StrikeEagleCC/ISU_ITec_Custom_CR-10/Arduino Windows Preconfigured/examples/01.Basics/DigitalReadSerial/layout.png

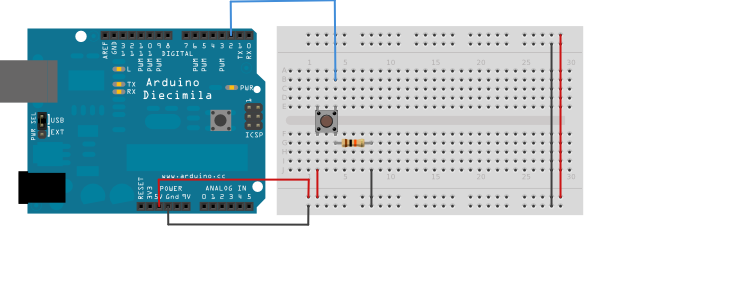
Arduino Windows Preconfigured/examples/01.Basics/DigitalReadSerial/layout.png
