StrikeEagleCC/ISU_ITec_Custom_CR-10/Arduino Windows Preconfigured/examples/01.Basics/Fade/layout.png

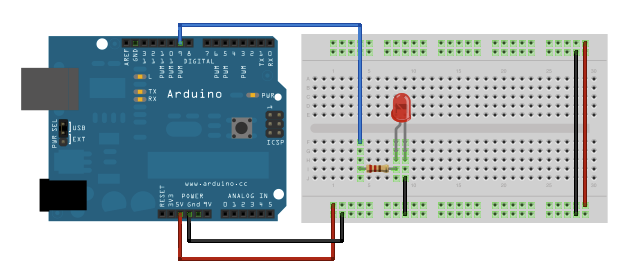
Arduino Windows Preconfigured/examples/01.Basics/Fade/layout.png
