StrikeEagleCC/ISU_ITec_Custom_CR-10/Arduino Windows Preconfigured/examples/02.Digital/toneKeyboard/schematic.png

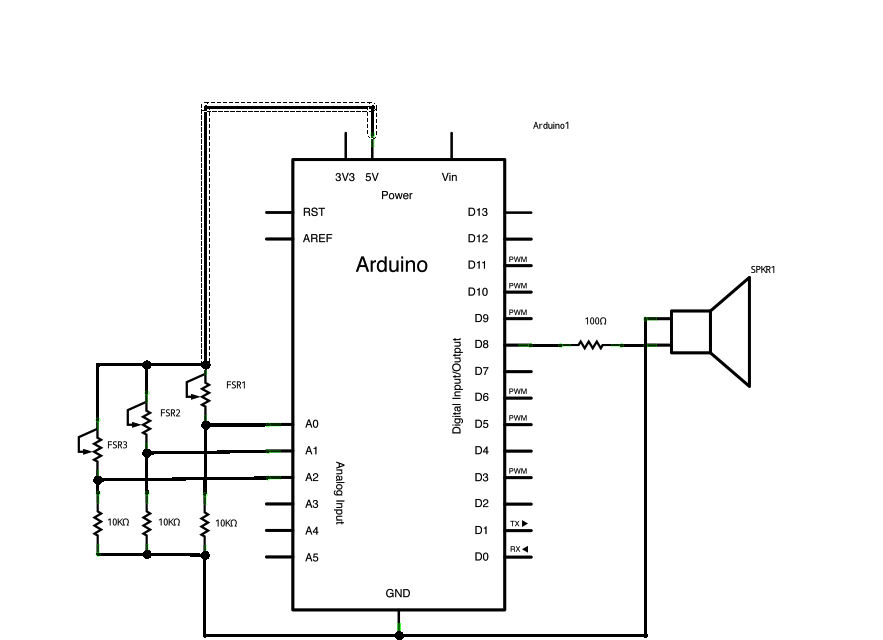
Arduino Windows Preconfigured/examples/02.Digital/toneKeyboard/schematic.png
