StrikeEagleCC/ISU_ITec_Custom_CR-10/Arduino Windows Preconfigured/examples/03.Analog/AnalogInOutSerial/schematic.png

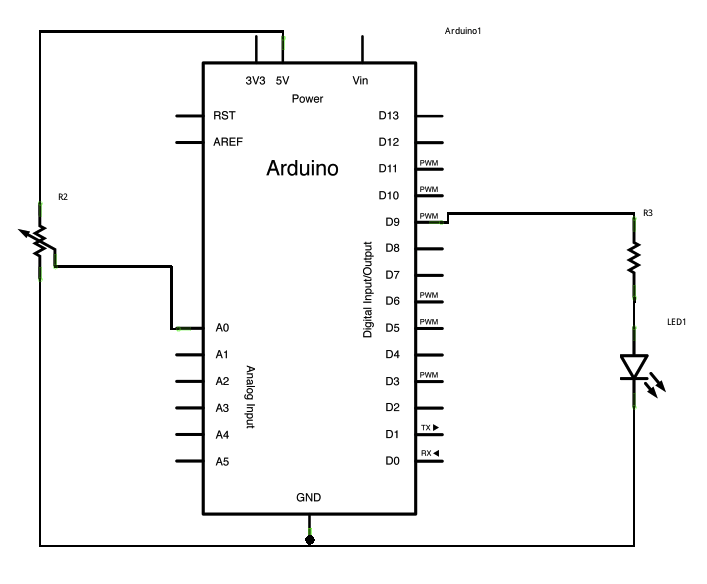
Arduino Windows Preconfigured/examples/03.Analog/AnalogInOutSerial/schematic.png
