StrikeEagleCC/ISU_ITec_Custom_CR-10/Arduino Windows Preconfigured/examples/03.Analog/AnalogWriteMega/schematic.png

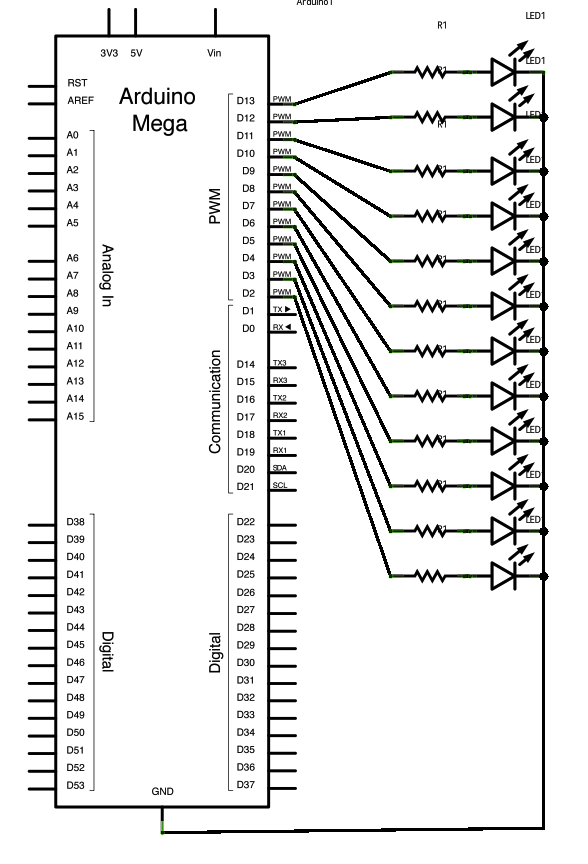
Arduino Windows Preconfigured/examples/03.Analog/AnalogWriteMega/schematic.png
