StrikeEagleCC/ISU_ITec_Custom_CR-10/Arduino Windows Preconfigured/examples/04.Communication/Midi/layout.png

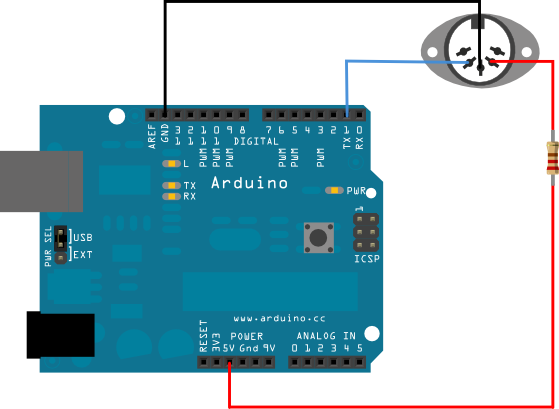
Arduino Windows Preconfigured/examples/04.Communication/Midi/layout.png
