StrikeEagleCC/ISU_ITec_Custom_CR-10/Arduino Windows Preconfigured/examples/05.Control/IfStatementConditional/schematic.png

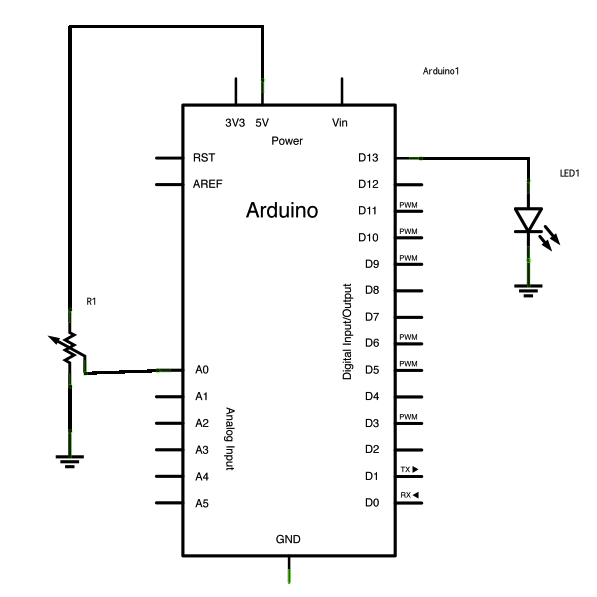
Arduino Windows Preconfigured/examples/05.Control/IfStatementConditional/schematic.png
