StrikeEagleCC/ISU_ITec_Custom_CR-10/Arduino Windows Preconfigured/examples/05.Control/switchCase2/layout.png

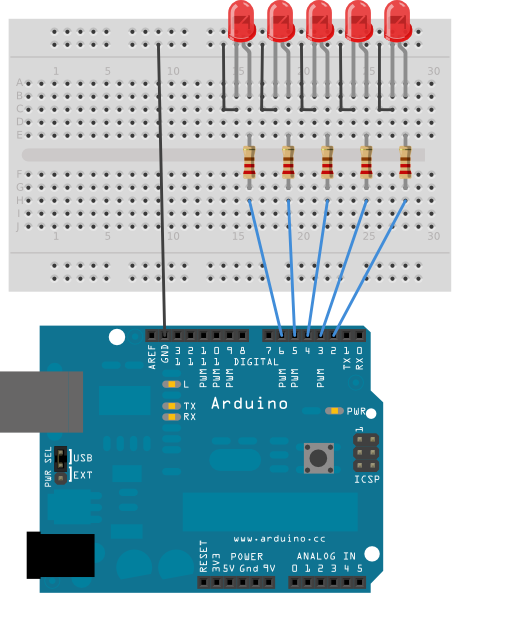
Arduino Windows Preconfigured/examples/05.Control/switchCase2/layout.png
