StrikeEagleCC/ISU_ITec_Custom_CR-10/Arduino Windows Preconfigured/examples/05.Control/switchCase/layout.png

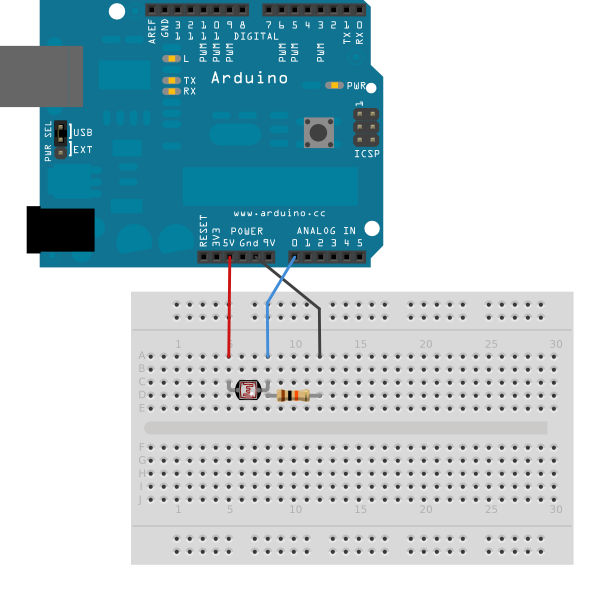
Arduino Windows Preconfigured/examples/05.Control/switchCase/layout.png
