StrikeEagleCC/ISU_ITec_Custom_CR-10/Arduino Windows Preconfigured/examples/06.Sensors/ADXL3xx/schematic.png

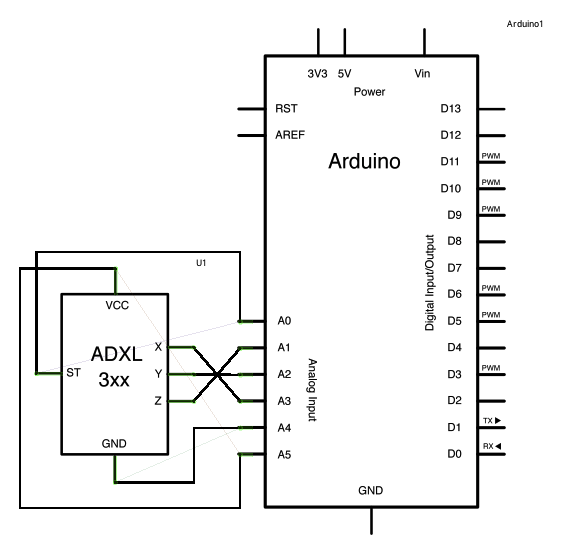
Arduino Windows Preconfigured/examples/06.Sensors/ADXL3xx/schematic.png
