StrikeEagleCC/ISU_ITec_Custom_CR-10/Arduino Windows Preconfigured/examples/07.Display/barGraph/layout.png

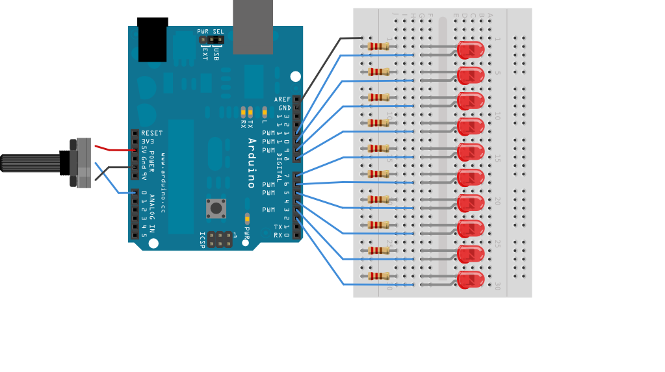
Arduino Windows Preconfigured/examples/07.Display/barGraph/layout.png
