StrikeEagleCC/ISU_ITec_Custom_CR-10/Arduino Windows Preconfigured/examples/07.Display/RowColumnScanning/layout.png

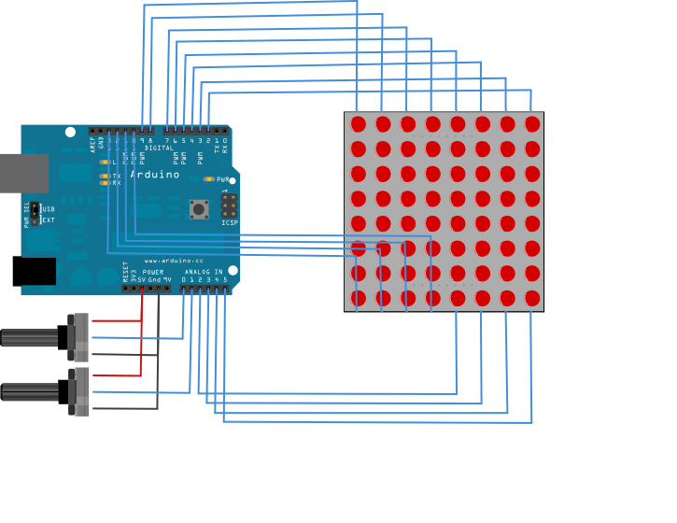
Arduino Windows Preconfigured/examples/07.Display/RowColumnScanning/layout.png
