StrikeEagleCC/ISU_ITec_Custom_CR-10/Arduino Windows Preconfigured/examples/07.Display/RowColumnScanning/schematic.png

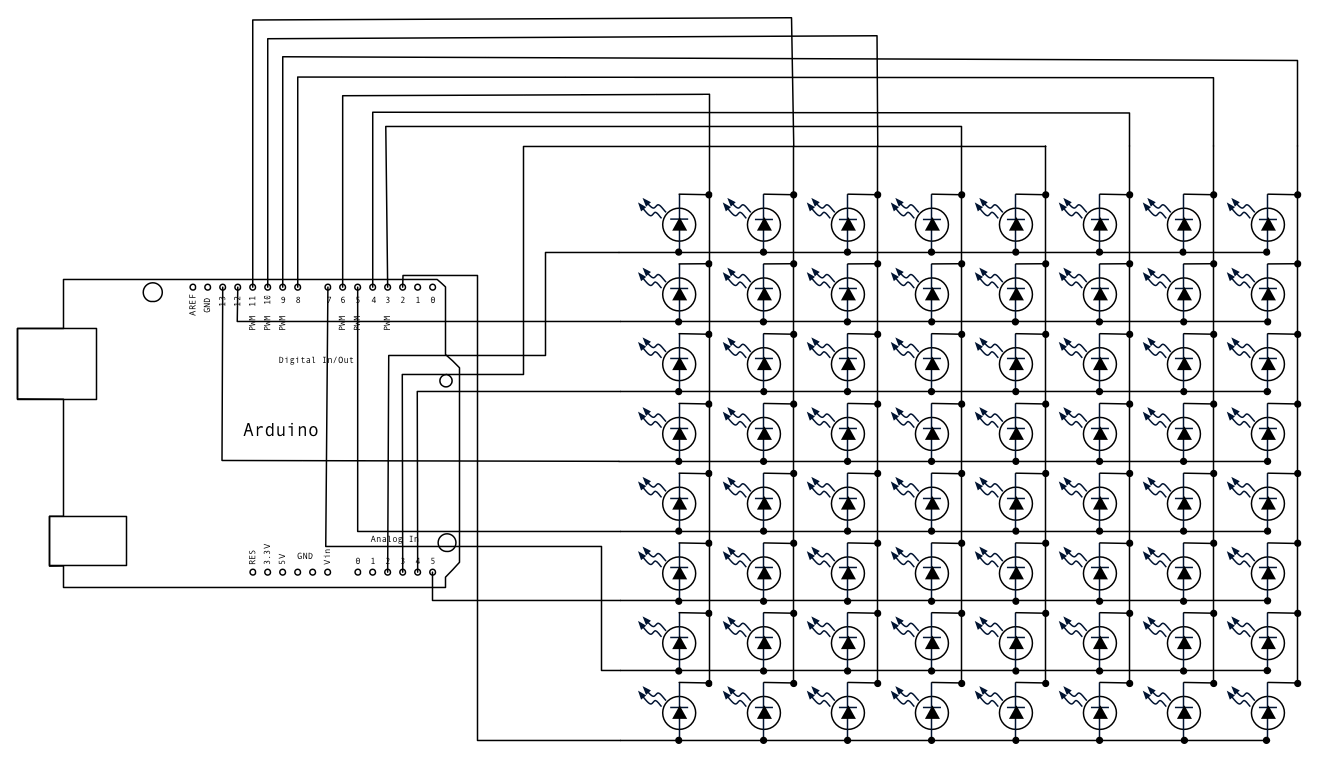
Arduino Windows Preconfigured/examples/07.Display/RowColumnScanning/schematic.png
