StrikeEagleCC/ISU_ITec_Custom_CR-10/Arduino Windows Preconfigured/examples/09.USB/KeyboardAndMouseControl/layout.png

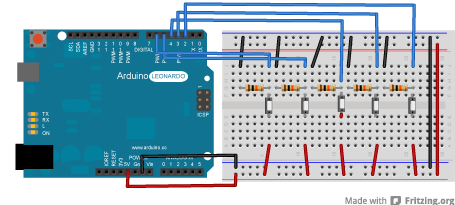
Arduino Windows Preconfigured/examples/09.USB/KeyboardAndMouseControl/layout.png
