StrikeEagleCC/ISU_ITec_Custom_CR-10/Arduino Windows Preconfigured/examples/09.USB/Mouse/JoystickMouseControl/schematic.png

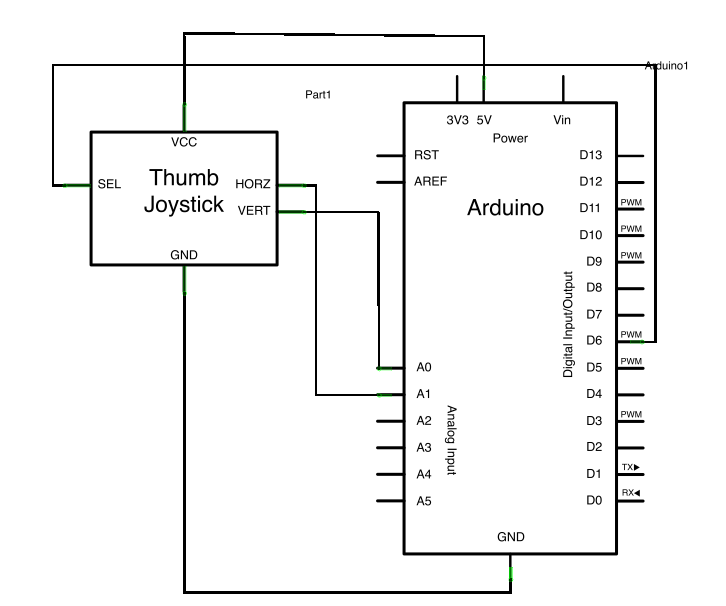
Arduino Windows Preconfigured/examples/09.USB/Mouse/JoystickMouseControl/schematic.png
