StrikeEagleCC/ISU_ITec_Custom_CR-10/Arduino Windows Preconfigured/reference/Edison_help_files/img7.jpg

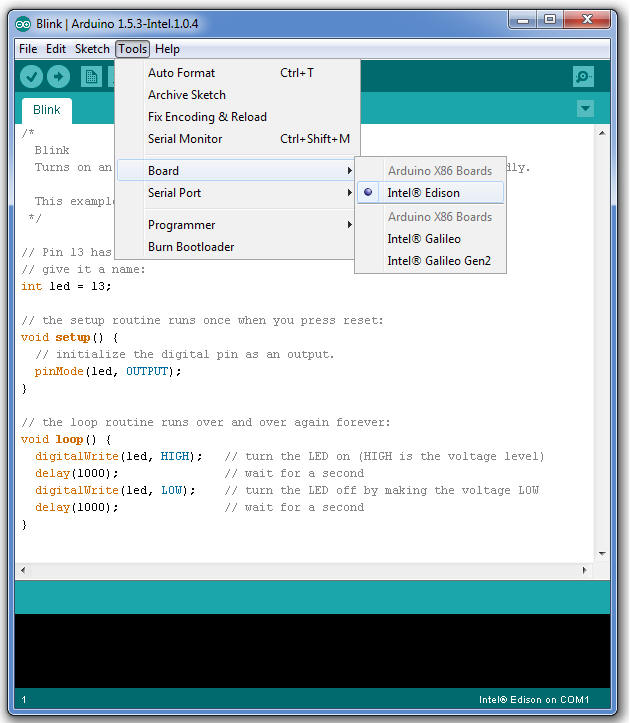
Arduino Windows Preconfigured/reference/Edison_help_files/img7.jpg
