StrikeEagleCC/ISU_ITec_Custom_CR-10/Arduino Windows Preconfigured/reference/Edison_help_files/imgE.gif

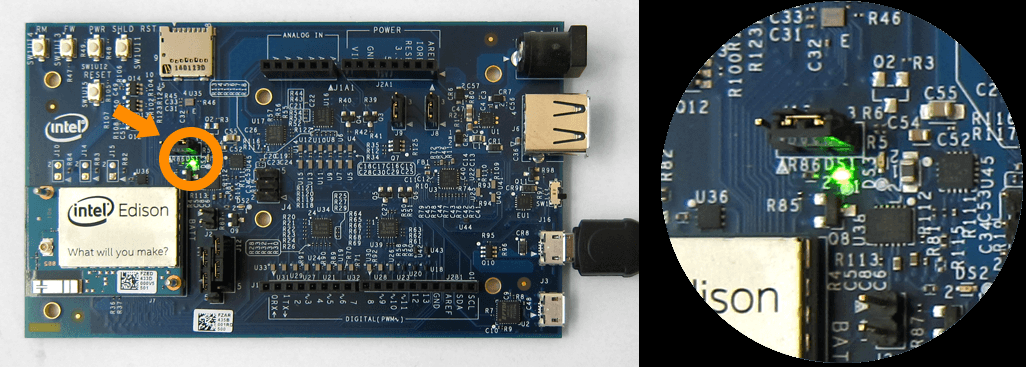
Arduino Windows Preconfigured/reference/Edison_help_files/imgE.gif
