StrikeEagleCC/ISU_ITec_Custom_CR-10/Arduino Windows Preconfigured/reference/Edison_help_files/linux_port_select.png

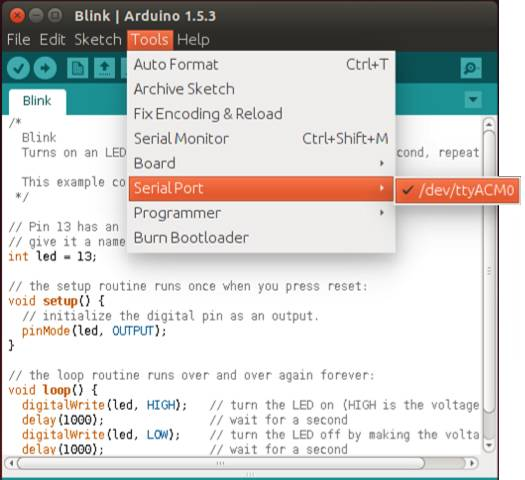
Arduino Windows Preconfigured/reference/Edison_help_files/linux_port_select.png
