StrikeEagleCC/ISU_ITec_Custom_CR-10/Arduino Windows Preconfigured/reference/Edison_help_files/single_usb_pic_jb.png

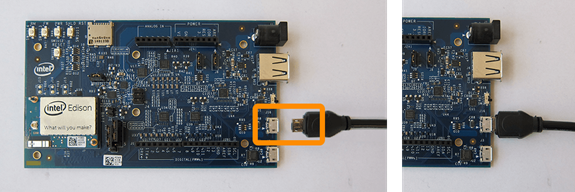
Arduino Windows Preconfigured/reference/Edison_help_files/single_usb_pic_jb.png
