StrikeEagleCC/ISU_ITec_Custom_CR-10/Arduino Windows Preconfigured/reference/Galileo_help_files/CAM00120.jpg

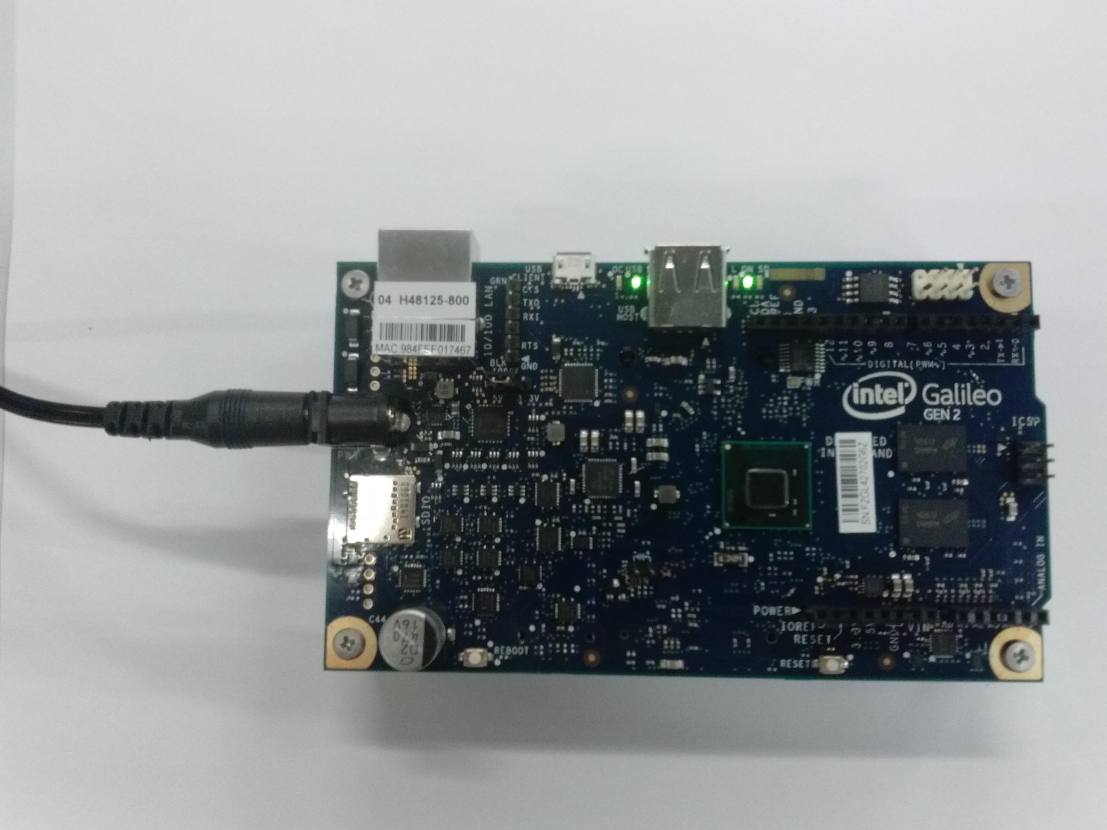
Arduino Windows Preconfigured/reference/Galileo_help_files/CAM00120.jpg
