StrikeEagleCC/ISU_ITec_Custom_CR-10/Arduino Windows Preconfigured/reference/Galileo_help_files/gal-power-supply.jpg

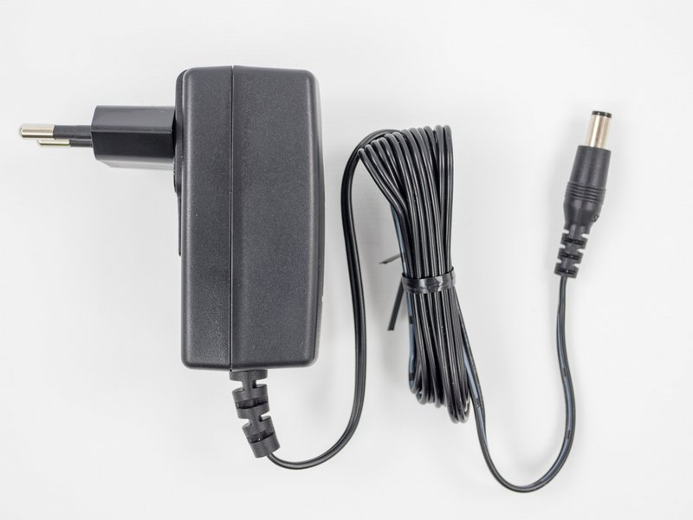
Arduino Windows Preconfigured/reference/Galileo_help_files/gal-power-supply.jpg
