StrikeEagleCC/ISU_ITec_Custom_CR-10/Arduino Windows Preconfigured/reference/Galileo_help_files/galileo-motherboard.jpg

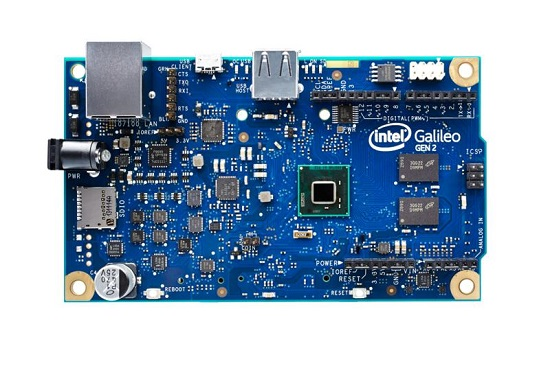
Arduino Windows Preconfigured/reference/Galileo_help_files/galileo-motherboard.jpg
