StrikeEagleCC/ISU_ITec_Custom_CR-10/Arduino Windows Preconfigured/reference/Galileo_help_files/galileo_port_device_manager.png

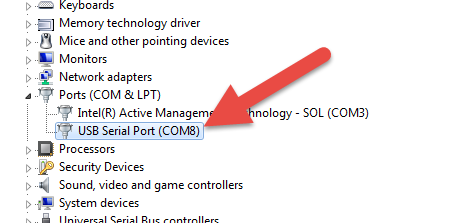
Arduino Windows Preconfigured/reference/Galileo_help_files/galileo_port_device_manager.png
