StrikeEagleCC/ISU_ITec_Custom_CR-10/Arduino Windows Preconfigured/reference/Galileo_help_files/select_galileo_board.png

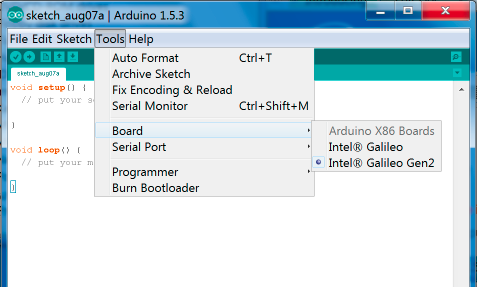
Arduino Windows Preconfigured/reference/Galileo_help_files/select_galileo_board.png
