StrikeEagleCC/ISU_ITec_Custom_CR-10/Arduino Windows Preconfigured/reference/www.arduino.cc/en/uploads/Main/ArduinoUno_R3_Front_450px.jpg

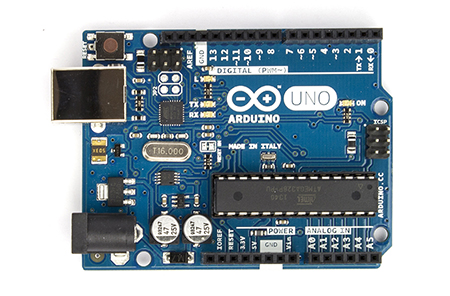
Arduino Windows Preconfigured/reference/www.arduino.cc/en/uploads/Main/ArduinoUno_R3_Front_450px.jpg
