StrikeEagleCC/ISU_ITec_Custom_CR-10/Arduino Windows Preconfigured/reference/www.arduino.cc/en/uploads/Reference/arduino_uno_ethernet_pins.png

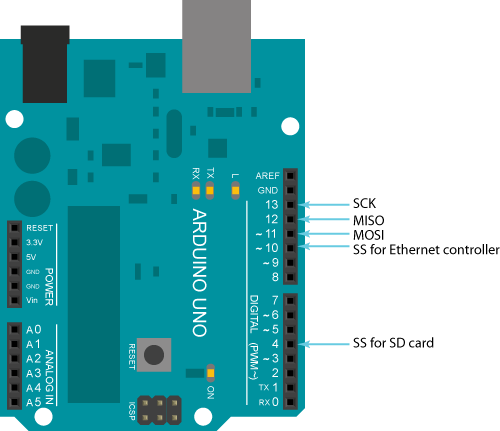
Arduino Windows Preconfigured/reference/www.arduino.cc/en/uploads/Reference/arduino_uno_ethernet_pins.png
