StrikeEagleCC/ISU_ITec_Custom_CR-10/Arduino Windows Preconfigured/reference/www.arduino.cc/en/uploads/Reference/arduinoEthernetShieldSD.jpg

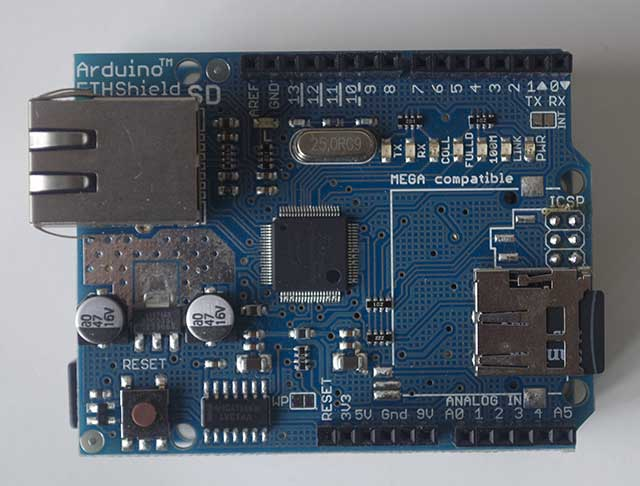
Arduino Windows Preconfigured/reference/www.arduino.cc/en/uploads/Reference/arduinoEthernetShieldSD.jpg
