StrikeEagleCC/ISU_ITec_Custom_CR-10/Arduino Windows Preconfigured/reference/www.arduino.cc/en/uploads/Reference/bipolar_stepper_four_pins.jpg

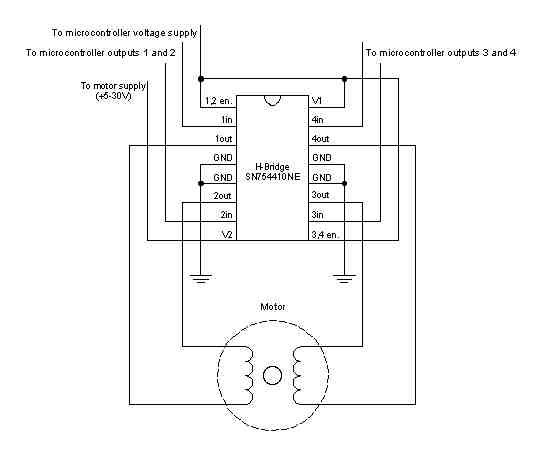
Arduino Windows Preconfigured/reference/www.arduino.cc/en/uploads/Reference/bipolar_stepper_four_pins.jpg
