StrikeEagleCC/ISU_ITec_Custom_CR-10/Arduino Windows Preconfigured/reference/www.arduino.cc/en/uploads/Reference/unipolar_stepper_two_pins.png

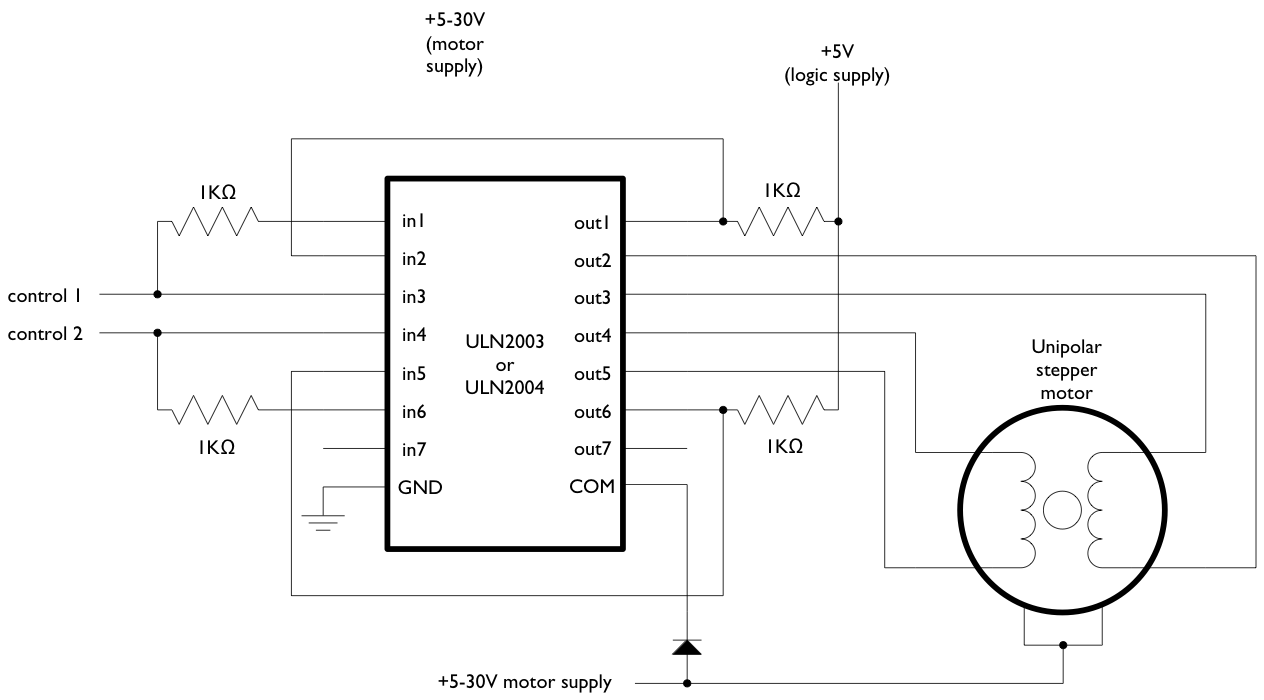
Arduino Windows Preconfigured/reference/www.arduino.cc/en/uploads/Reference/unipolar_stepper_two_pins.png
