StrikeEagleCC/ISU_ITec_Custom_CR-10/Arduino Windows Preconfigured/reference/www.arduino.cc/en/uploads/Guide/languagePreferences.png

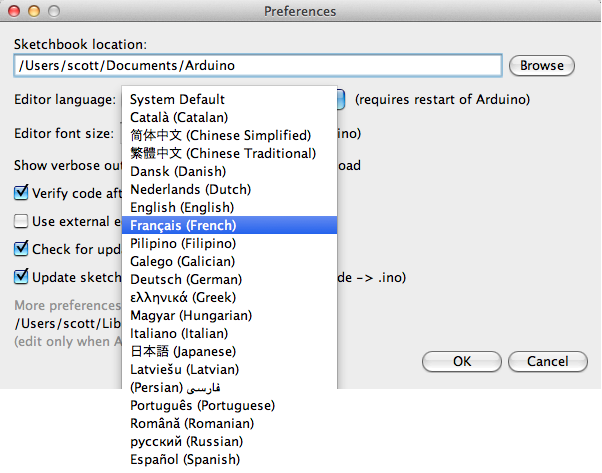
Arduino Windows Preconfigured/reference/www.arduino.cc/en/uploads/Guide/languagePreferences.png
