StrikeEagleCC/ISU_ITec_Custom_CR-10/Arduino Windows Preconfigured/examples/03.Analog/Calibration/layout.png

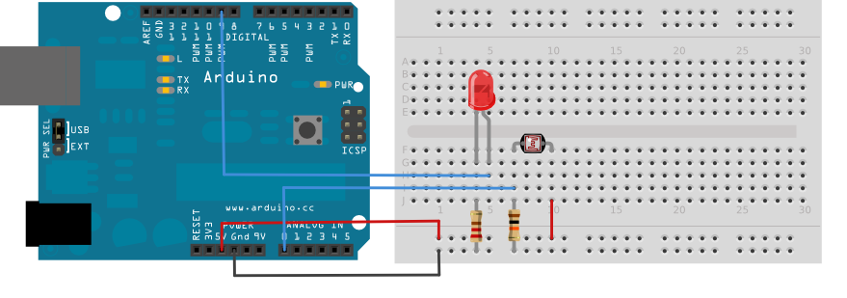
Arduino Windows Preconfigured/examples/03.Analog/Calibration/layout.png
